telepath9/ESPclock/pics/demo.png

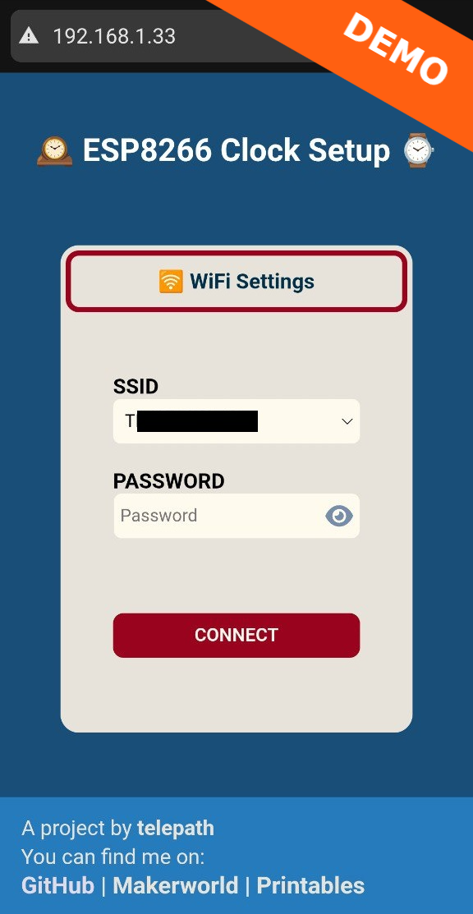
pics/demo.png
