telepath9/ESPclock/pics/NEW_json_structure.jpg

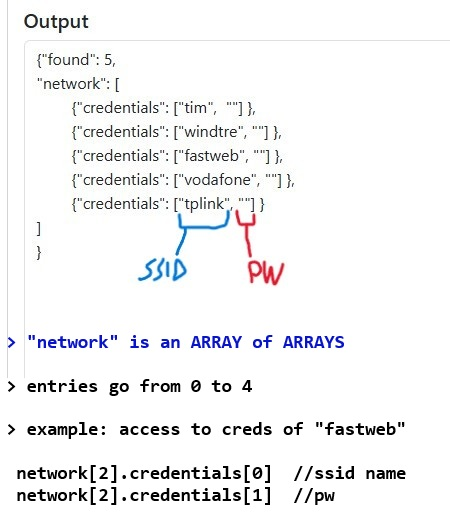
pics/NEW_json_structure.jpg
