telepath9/ESPclock/pics/title.png

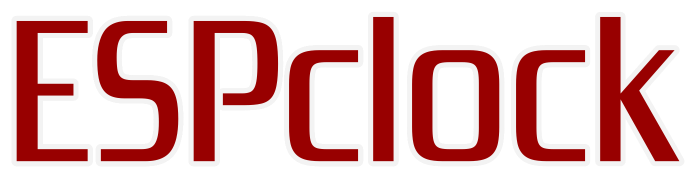
pics/title.png
