telepath9/ESPclock/pics/v2.0_new.jpg

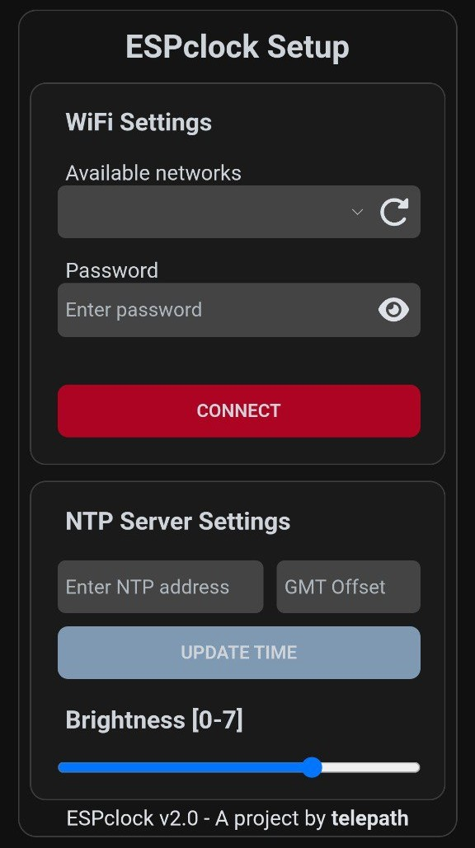
pics/v2.0_new.jpg
