telepath9/ESPclock/pics/v2.2.jpg

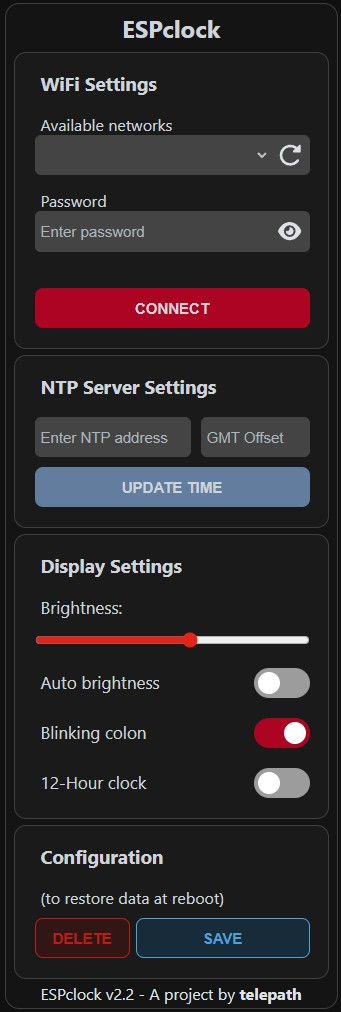
pics/v2.2.jpg
