telepath9/ESPclock/pics/v2.3.0.webp

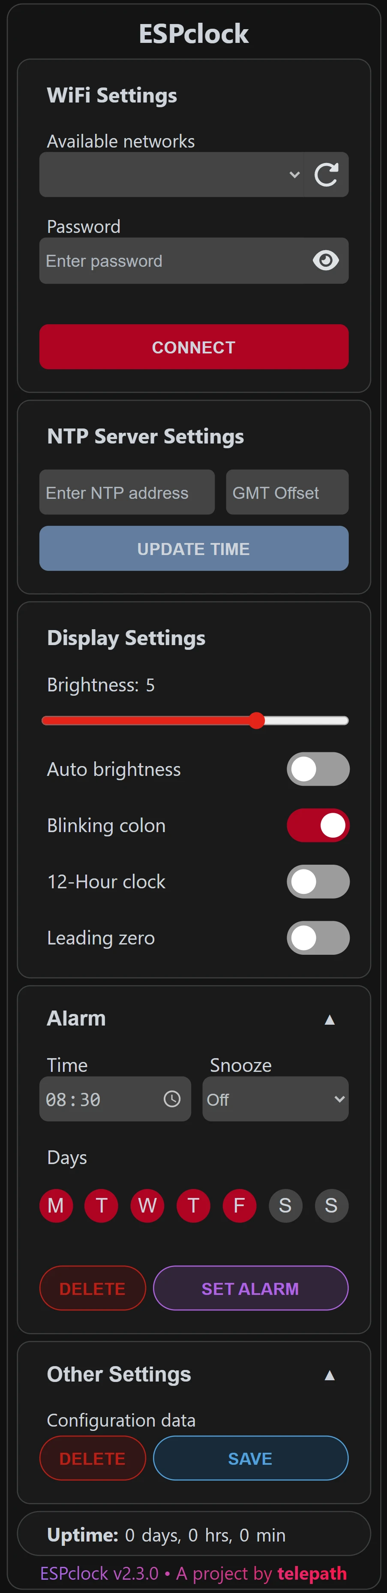
pics/v2.3.0.webp
